Batterhead221/game_girl/outputs/img/fab.jpeg

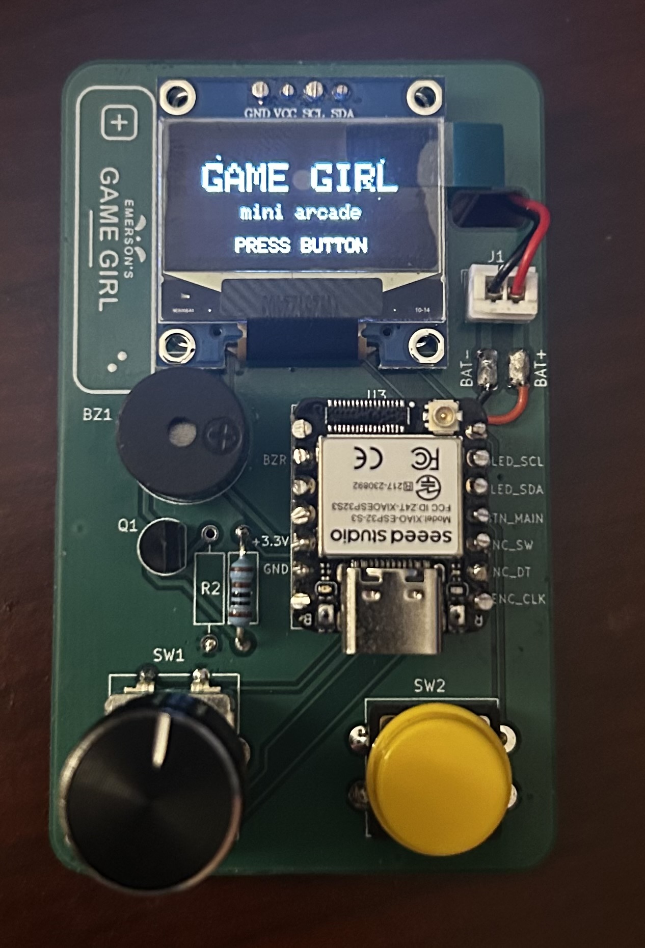
outputs/img/fab.jpeg
