Batterhead221/game_girl/outputs/img/3d.png

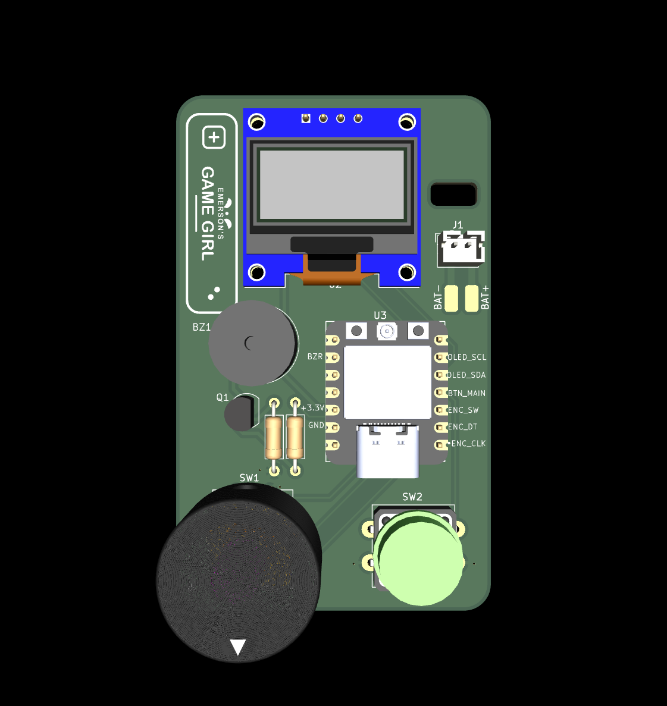
outputs/img/3d.png
