Batterhead221/game_girl/Outputs/IMG/L1.png

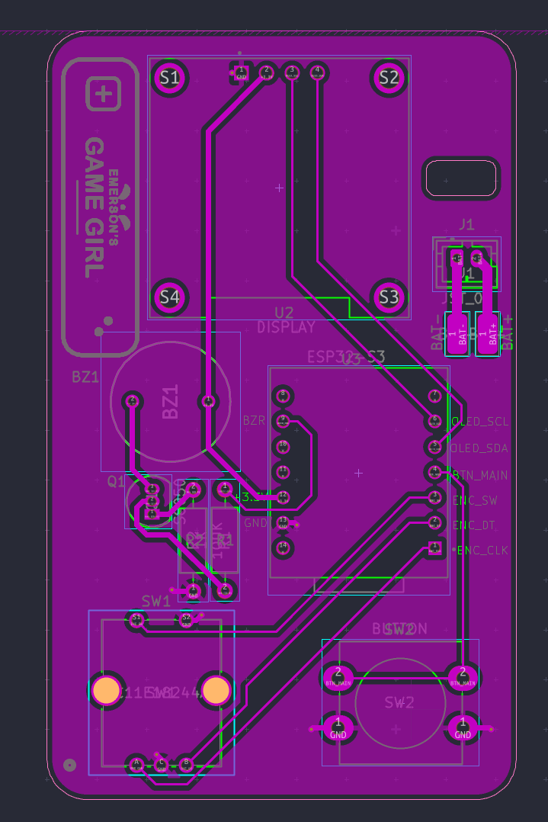
Outputs/IMG/L1.png
