Batterhead221/game_girl/Outputs/IMG/L2.png

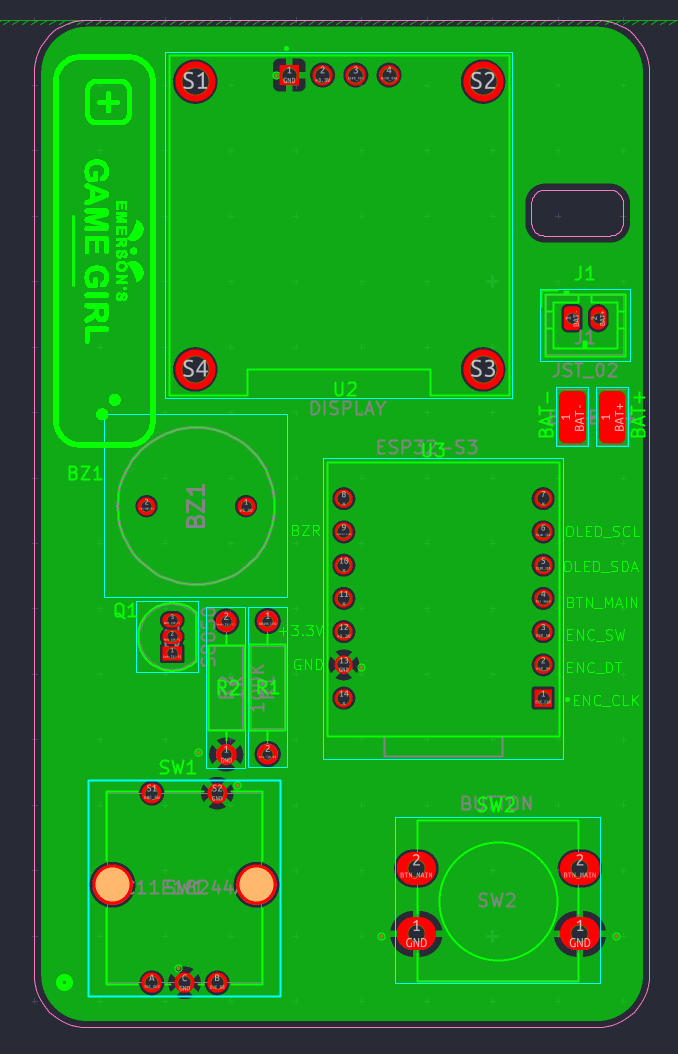
Outputs/IMG/L2.png
