Batterhead221/game_girl/Outputs/IMG/SCHEMATIC.png

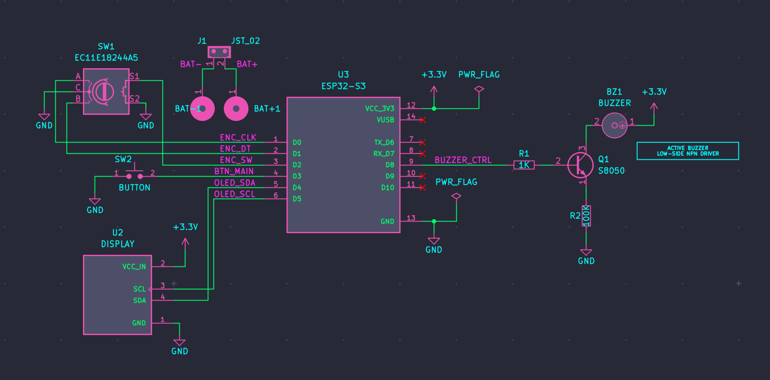
Outputs/IMG/SCHEMATIC.png
